bartczechov205/ApexIO_Firmware/include/Macro.h

#pragma once

#define GPS_SERIAL Serial1
#define GPS_BAUDRATE 38400
#define GPS_FREQUENCY 10
#define GPS_TX_PIN 17
#define GPS_RX_PIN 18

#define IMU_FREQUENCY 100
#define IMU_SCK 15
#define IMU_MISO 21
#define IMU_MOSI 16
#define IMU_CS 8
#define IMU_INT 1
#define IMU_RST 2

#define SD_CS   4
#define SD_MOSI 5
#define SD_MISO 6
#define SD_SCK  7
#define SD_DETECT_PIN 48

#define BTN_UP 47
#define BTN_DOWN 42
#define BTN_OK 40
#define BTN_BACK 39

#define TFT_BL 41

#define I2C_SDA 38
#define I2C_SCL 13

#define SD_DETECT_PIN 48
